mtrancossi/CEA-PR-Cheap-and-Easy-Assembly-Pandemic-Respirator/Image6.jpg

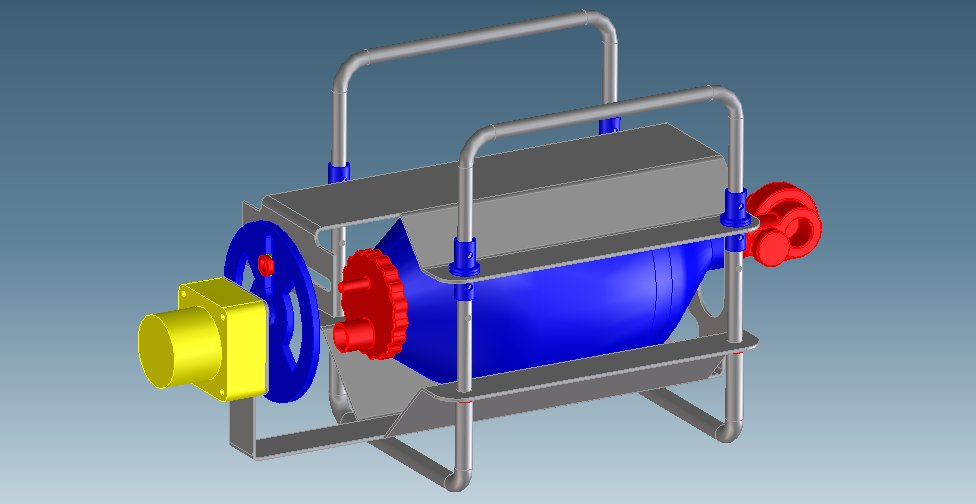
Image6.jpg
