mtrancossi/CEA-PR-Cheap-and-Easy-Assembly-Pandemic-Respirator/Image11.jpg

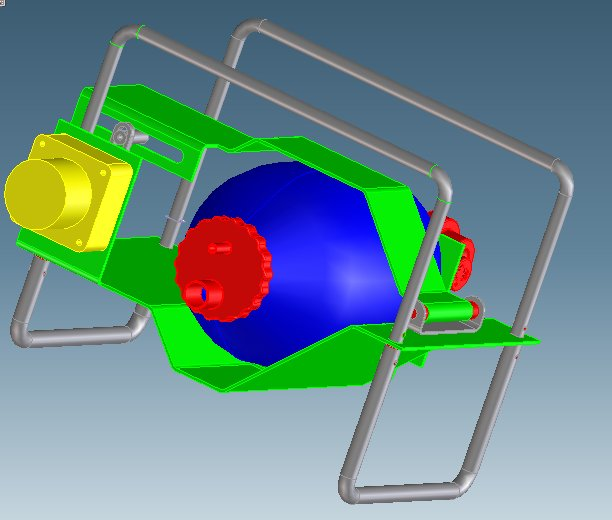
Image11.jpg
